lunderot/RGBClock/RGBClock/digitmap.h

//Maps numbers to 7-segment digits.
//Each digit is represented with one bit.
//Last bit is not used.
const char digitmap[] = {
	0b11101110,
	0b00000110,
	0b01111100,
	0b00111110,
	0b10010110,
	0b10111010,
	0b11111010,
	0b00001110,
	0b11111110,
	0b10111110
};
